yeokm1/pcb-name-card-sp/sp-designs-rebrand/sp-digital.bmp

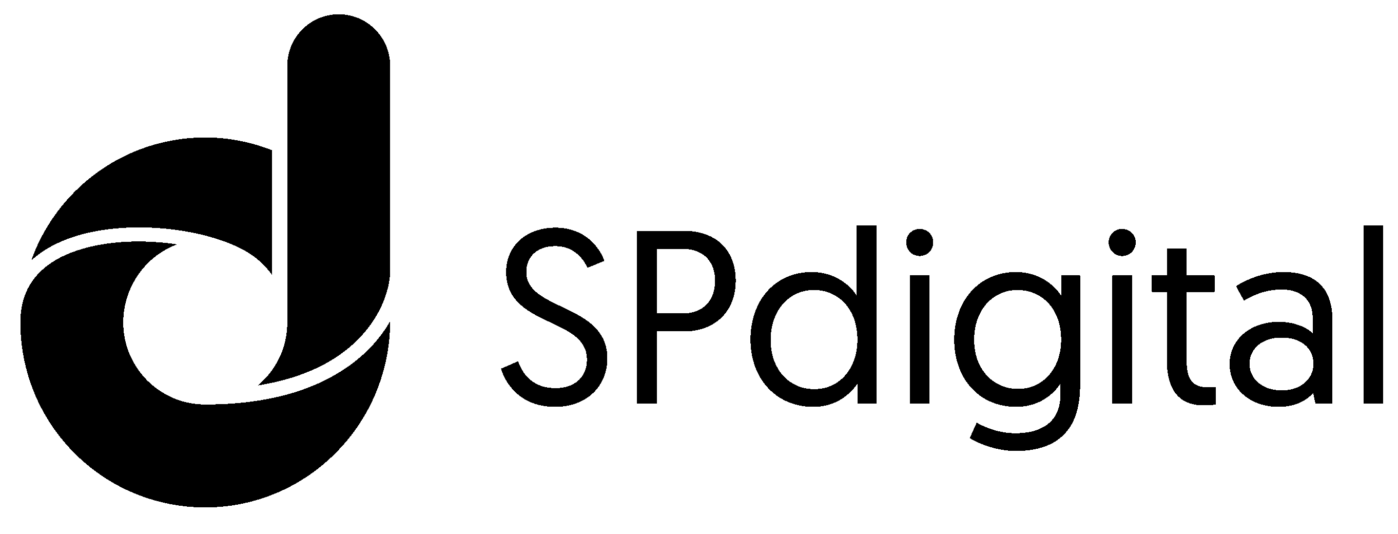
sp-designs-rebrand/sp-digital.bmp
